euvalennn/beagle/pcb/assets/bfp.png

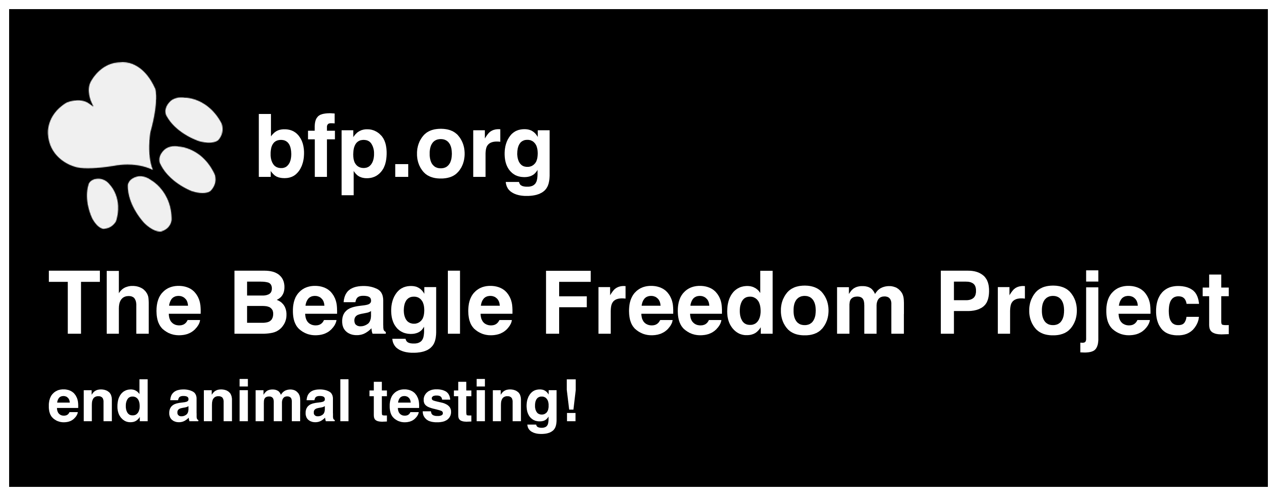
pcb/assets/bfp.png
