euvalennn/beagle/pcb/assets/borders.png

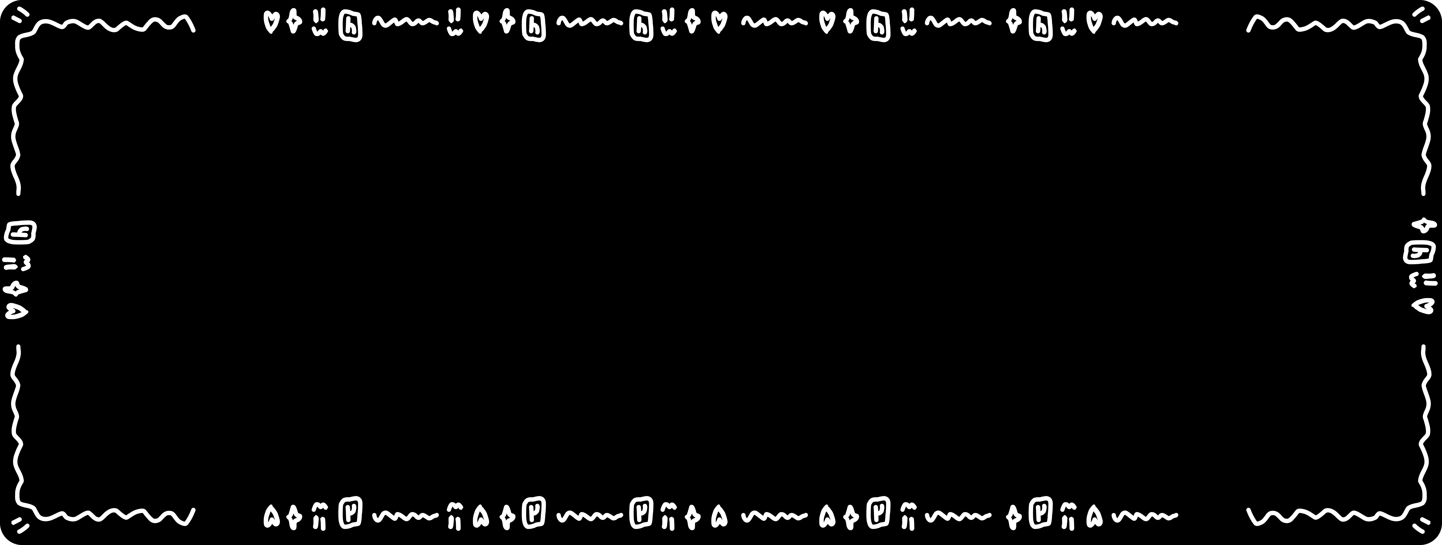
pcb/assets/borders.png
