euvalennn/beagle/pcb/assets/front.png

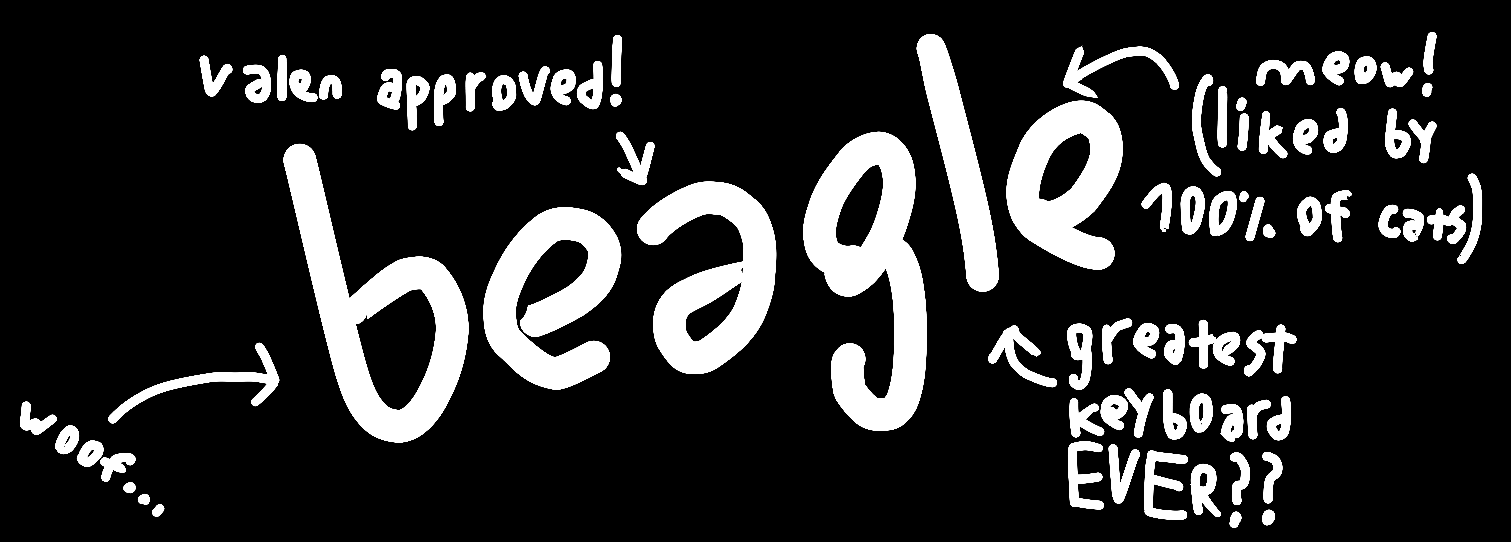
pcb/assets/front.png
