euvalennn/beagle/pcb/assets/stickers.png

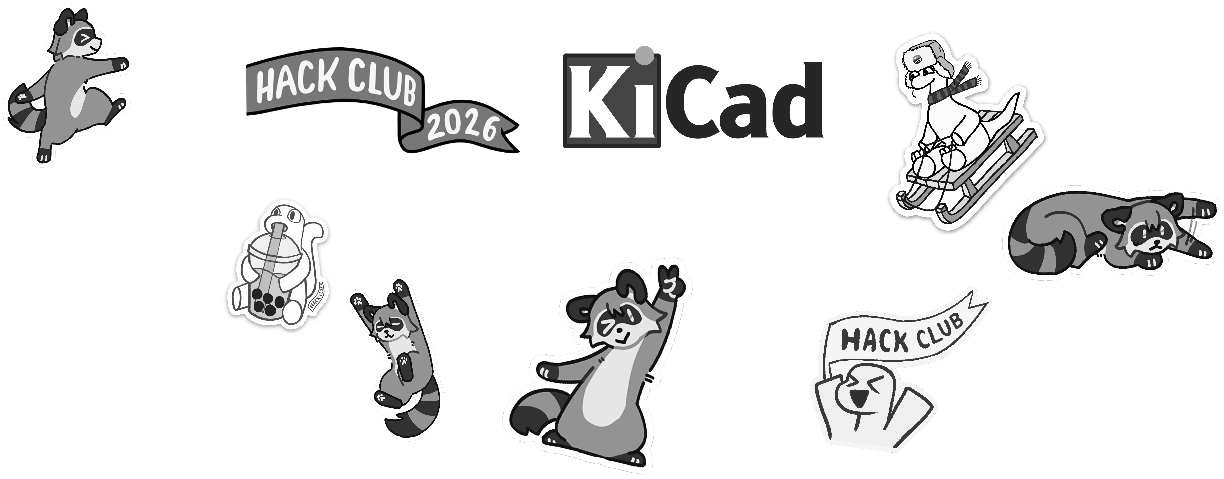
pcb/assets/stickers.png
