euvalennn/beagle/pcb/assets/was here!.png

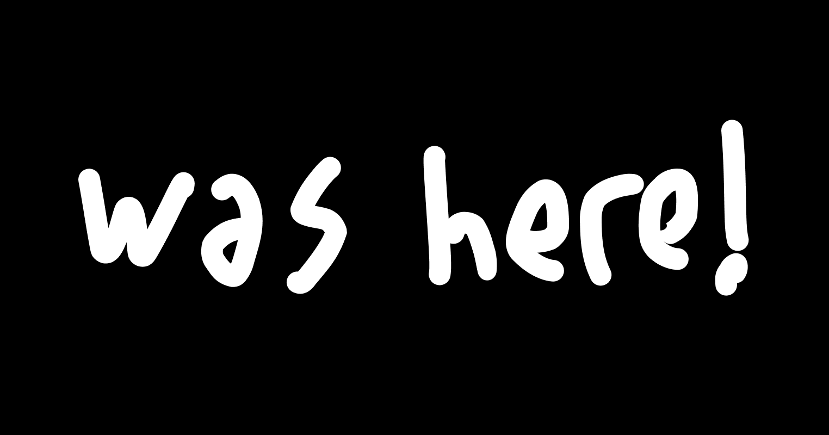
pcb/assets/was here!.png
