euvalennn/beagle/pcb/assets/3dmodels/0.91in OLED Module - Without Glass.stp

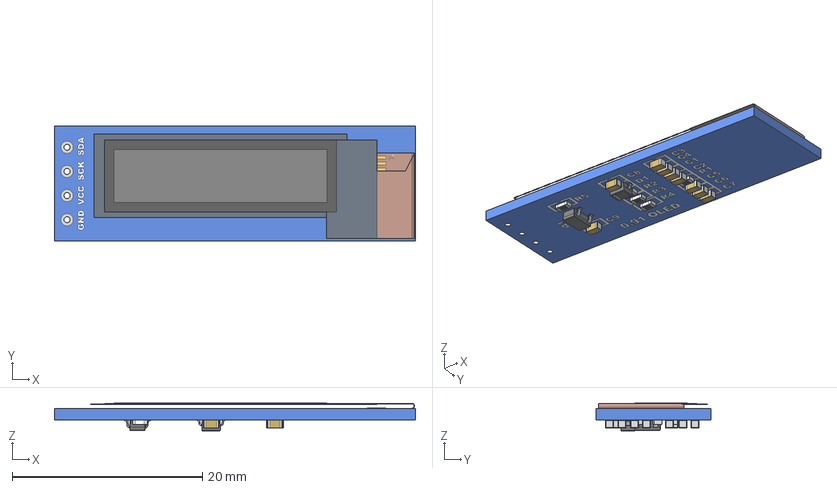
[picture p34: CAD file, 2026-06-26]
pcb/assets/3dmodels/0.91in OLED Module - Without Glass.stp
37.9 x 12.1 x 2.93 mm
0.91in oled Module - Board
0.91in OLED - Folded Flush - Without Glass
0603 Capacitor x 9
0603 Resistor x 5
SOT23-3
Diode (SOD-323)
