euvalennn/beagle/pcb/assets/3dmodels/2-54mm-male-pin-header/Step/100mill Male Pin Header_8P_Bk.STEP

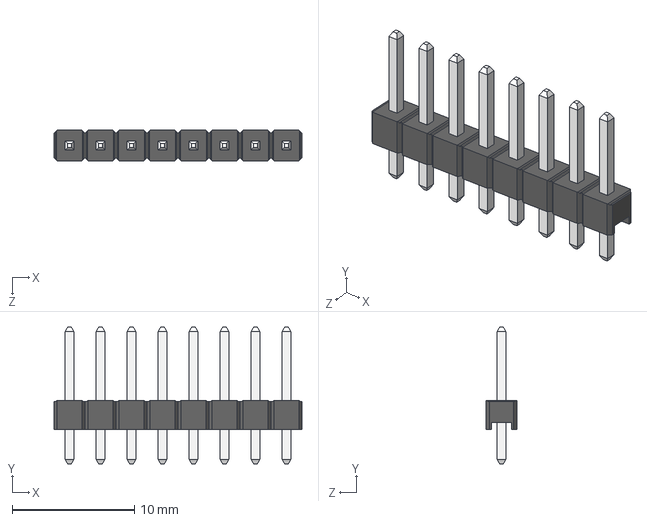
[picture p35: CAD file, 2026-06-26]
pcb/assets/3dmodels/2-54mm-male-pin-header/Step/100mill Male Pin Header_8P_Bk.STEP
20.3 x 11.2 x 2.50 mm
