euvalennn/beagle/pcb/assets/3dmodels/cherry_mx_keycaps/r3/r3_100_bar.STEP

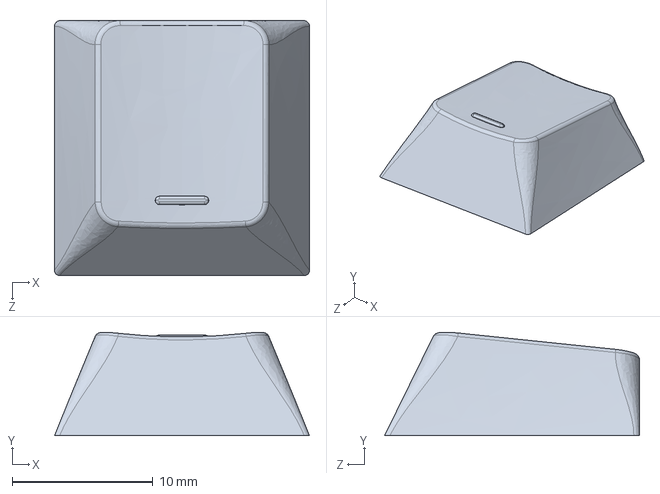
[picture p36: CAD file, 2026-06-26]
pcb/assets/3dmodels/cherry_mx_keycaps/r3/r3_100_bar.STEP
18.1 x 7.34 x 18.1 mm
