euvalennn/beagle/pcb/assets/3dmodels/cherry_mx_keycaps/r4/r3-4_200vert.STEP

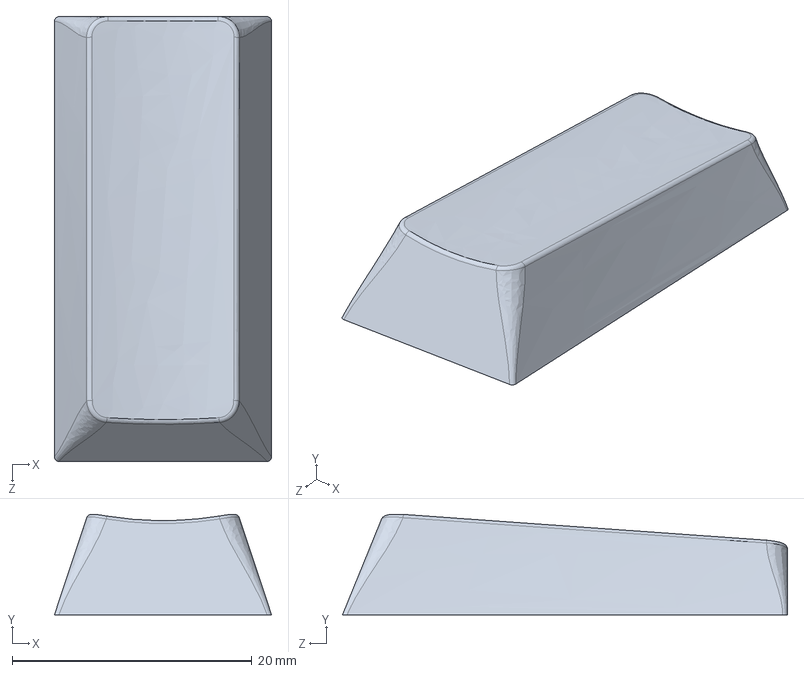
[picture p37: CAD file, 2026-06-26]
pcb/assets/3dmodels/cherry_mx_keycaps/r4/r3-4_200vert.STEP
18.1 x 8.38 x 37.1 mm
