euvalennn/beagle/production/top-case.stl

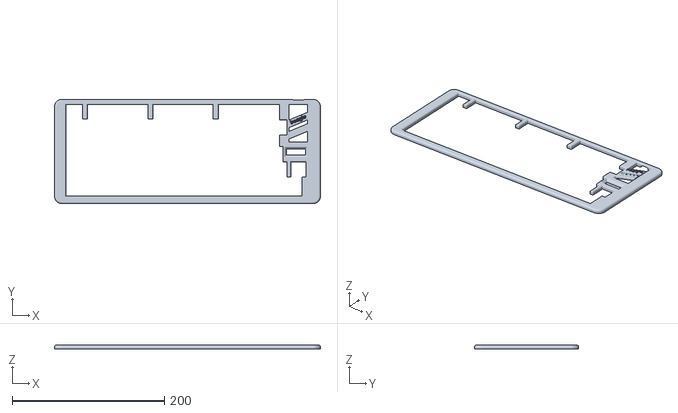
[picture p38: CAD file, 2026-06-26]
production/top-case.stl
349.0 x 137.1 x 5.00
