euvalennn/beagle/pcb/assets/3dmodels/2-54mm-male-pin-header/Step/100mill Male Pin Header_40P_Y.STEP

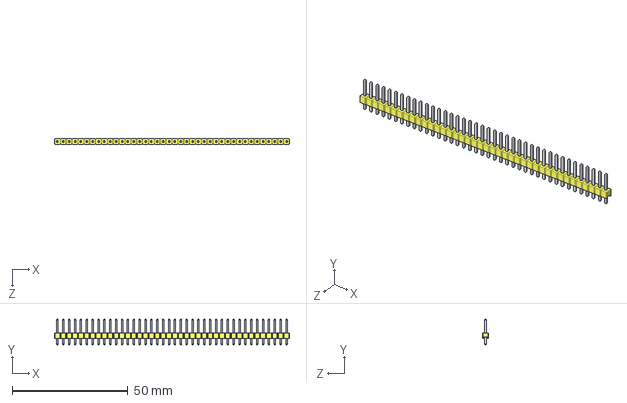
[picture p39: CAD file, 2026-06-26]
pcb/assets/3dmodels/2-54mm-male-pin-header/Step/100mill Male Pin Header_40P_Y.STEP
101.6 x 11.2 x 2.50 mm
