euvalennn/beagle/pcb/assets/3dmodels/cherry_mx_keycaps/r3/r3_200.STEP

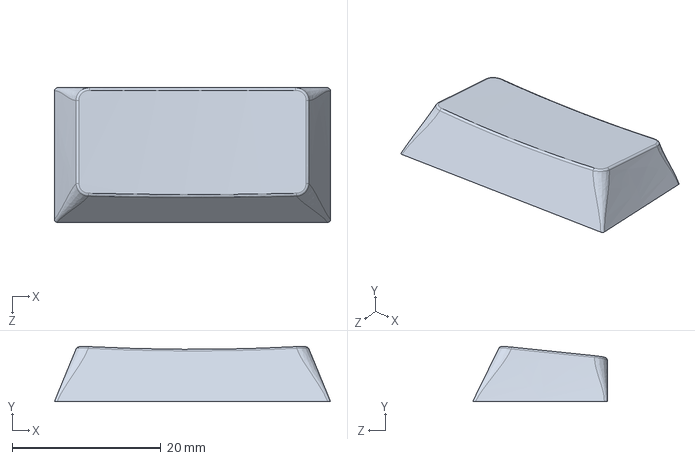
[picture p40: CAD file, 2026-06-26]
pcb/assets/3dmodels/cherry_mx_keycaps/r3/r3_200.STEP
37.1 x 7.40 x 18.1 mm
