euvalennn/beagle/pcb/assets/3dmodels/cherry_mx_keycaps/r4/r4_275C.step

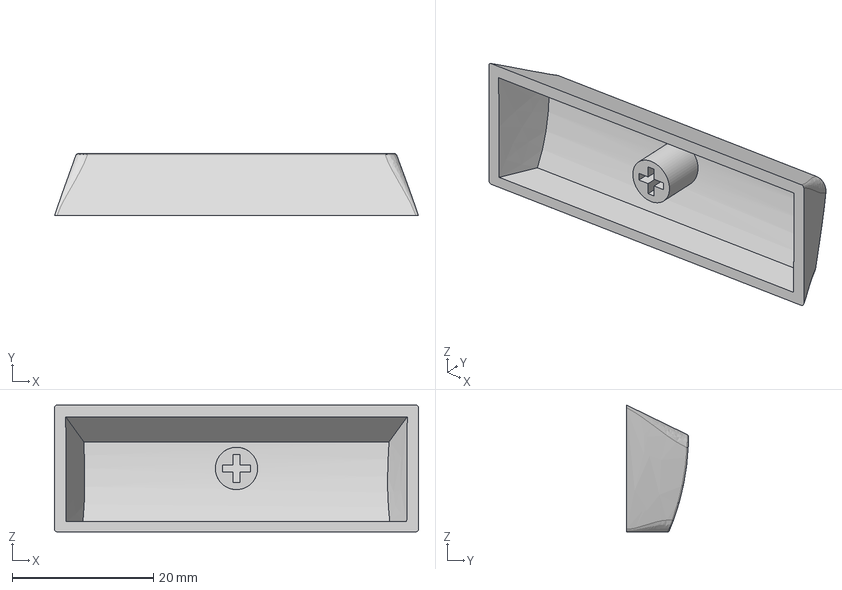
[picture p41: CAD file, 2026-06-26]
pcb/assets/3dmodels/cherry_mx_keycaps/r4/r4_275C.step
51.6 x 8.80 x 18.0 mm
