euvalennn/beagle/pcb/assets/3dmodels/hc-knob.step

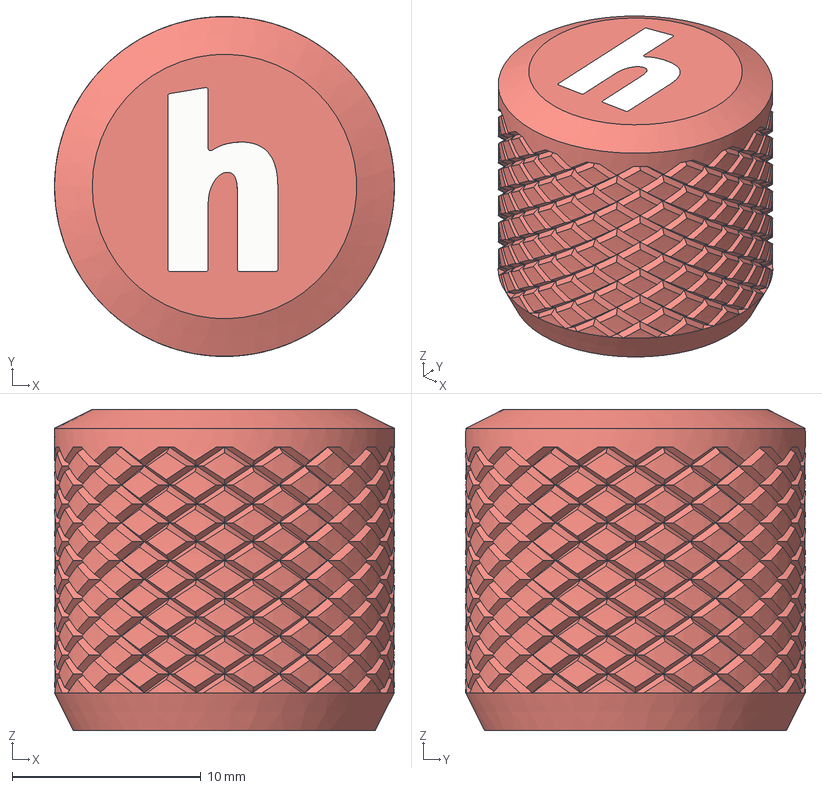
[picture p42: CAD file, 2026-06-26]
pcb/assets/3dmodels/hc-knob.step
18.0 x 18.0 x 17.0 mm
Base
H
