euvalennn/beagle/production/plate.stl

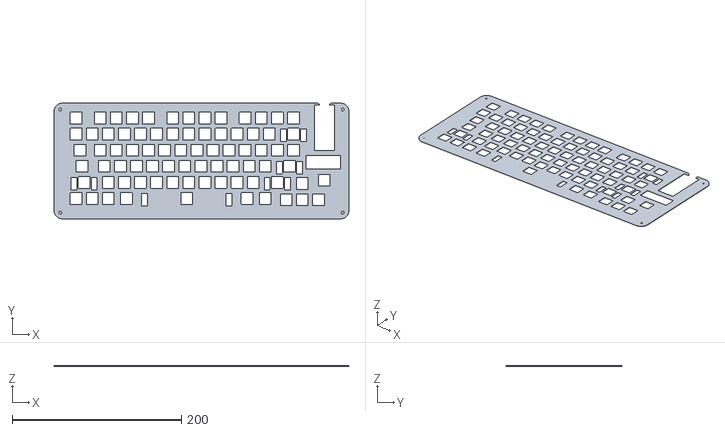
[picture p43: CAD file, 2026-06-26]
production/plate.stl
349.0 x 137.1 x 1.50
