euvalennn/beagle/pcb/assets/3dmodels/2-54mm-male-pin-header/Step/100mill Male Pin Header_4P_R.STEP

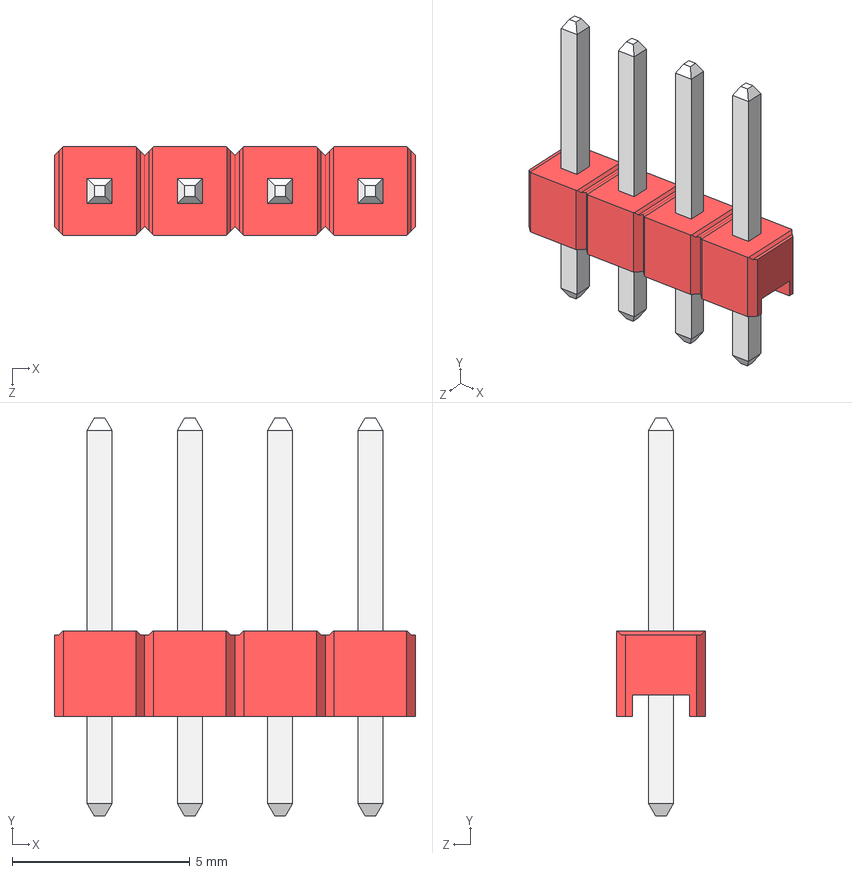
[picture p44: CAD file, 2026-06-26]
pcb/assets/3dmodels/2-54mm-male-pin-header/Step/100mill Male Pin Header_4P_R.STEP
10.2 x 11.2 x 2.50 mm
