euvalennn/beagle/pcb/assets/3dmodels/cherry_mx_keycaps/r4/r4_100.STEP

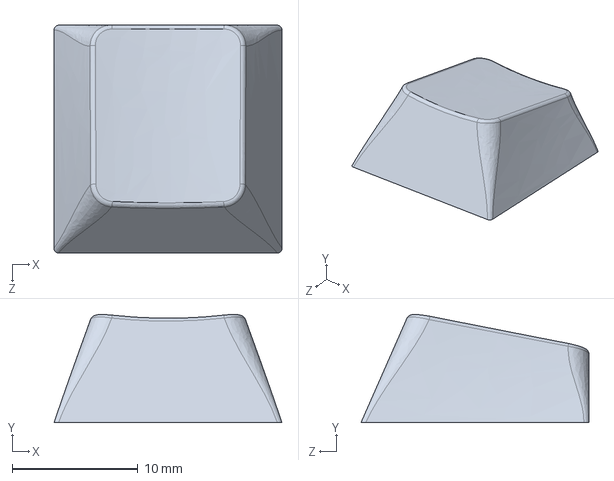
[picture p45: CAD file, 2026-06-26]
pcb/assets/3dmodels/cherry_mx_keycaps/r4/r4_100.STEP
18.1 x 8.58 x 18.1 mm
