euvalennn/beagle/pcb/assets/3dmodels/cherry_mx_keycaps/r3/r3_125.STEP

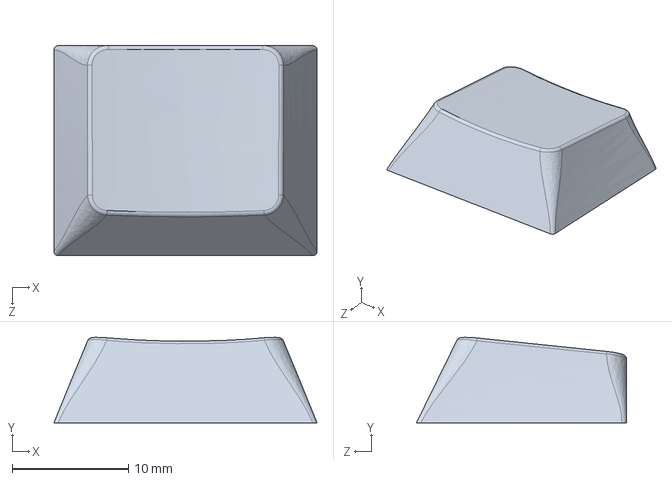
[picture p47: CAD file, 2026-06-26]
pcb/assets/3dmodels/cherry_mx_keycaps/r3/r3_125.STEP
22.7 x 7.36 x 18.1 mm
