euvalennn/beagle/pcb/assets/3dmodels/cherry_mx_keycaps/r4/r4_200C.step

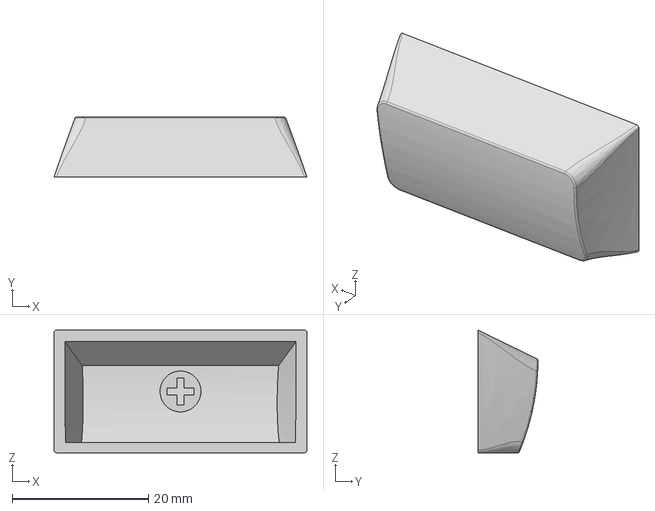
[picture p48: CAD file, 2026-06-26]
pcb/assets/3dmodels/cherry_mx_keycaps/r4/r4_200C.step
37.1 x 8.80 x 18.0 mm
