euvalennn/beagle/pcb/assets/3dmodels/cherry_mx_keycaps/r3/r3_iso.STEP

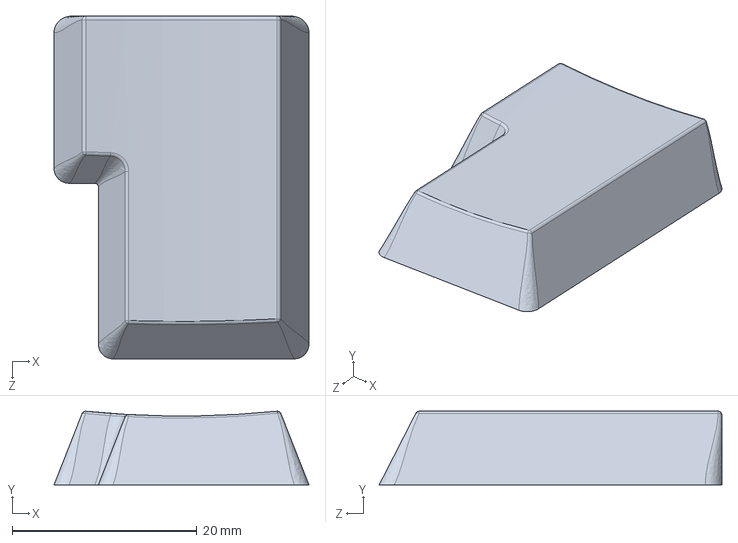
[picture p50: CAD file, 2026-06-26]
pcb/assets/3dmodels/cherry_mx_keycaps/r3/r3_iso.STEP
27.6 x 7.97 x 37.1 mm
