euvalennn/beagle/pcb/assets/3dmodels/cherry_mx_keycaps/r4/r4_100C.step

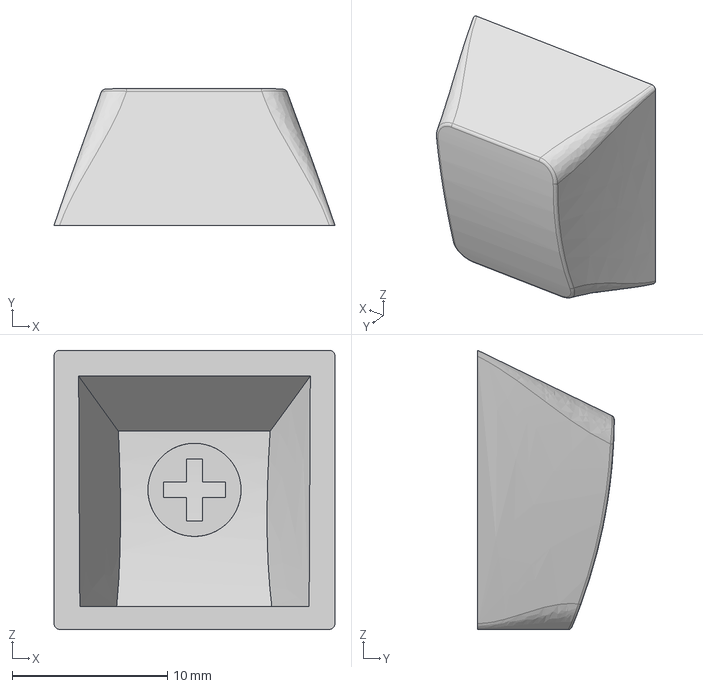
[picture p51: CAD file, 2026-06-26]
pcb/assets/3dmodels/cherry_mx_keycaps/r4/r4_100C.step
18.1 x 8.80 x 18.0 mm
