euvalennn/beagle/pcb/assets/3dmodels/cherry_mx_keycaps/r3/r3_175_stepped.STEP

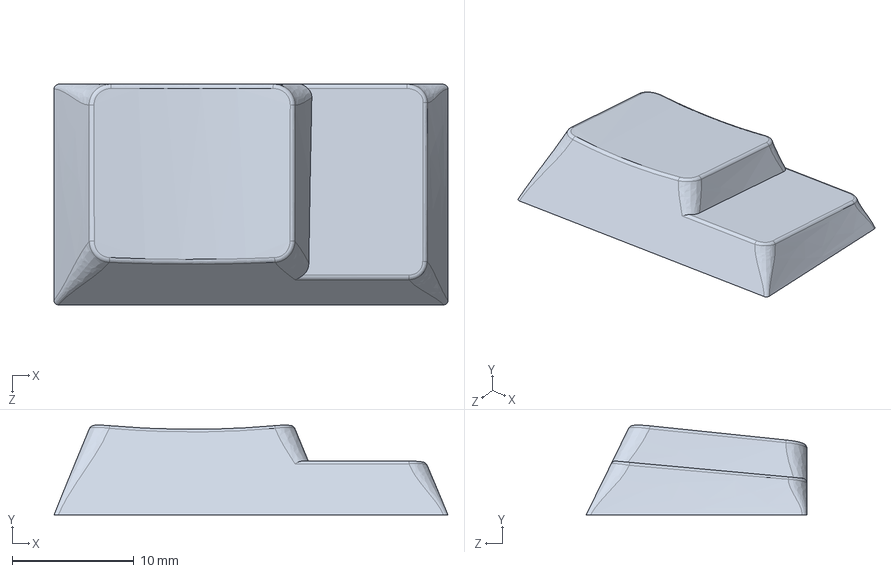
[picture p53: CAD file, 2026-06-26]
pcb/assets/3dmodels/cherry_mx_keycaps/r3/r3_175_stepped.STEP
32.3 x 7.36 x 18.1 mm
