euvalennn/beagle/pcb/assets/3dmodels/cherry_mx_keycaps/r4/r4_175.STEP

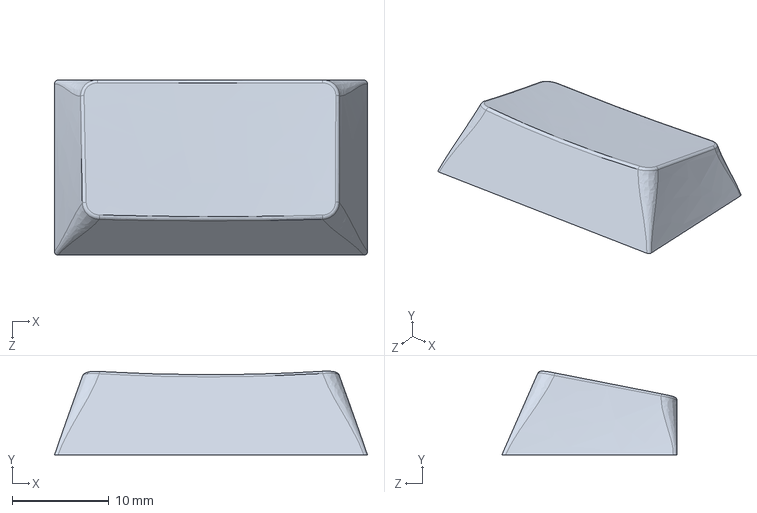
[picture p54: CAD file, 2026-06-26]
pcb/assets/3dmodels/cherry_mx_keycaps/r4/r4_175.STEP
32.3 x 8.65 x 18.1 mm
