euvalennn/beagle/pcb/assets/3dmodels/cherry_mx_keycaps/r3/r2-3_200vert.STEP

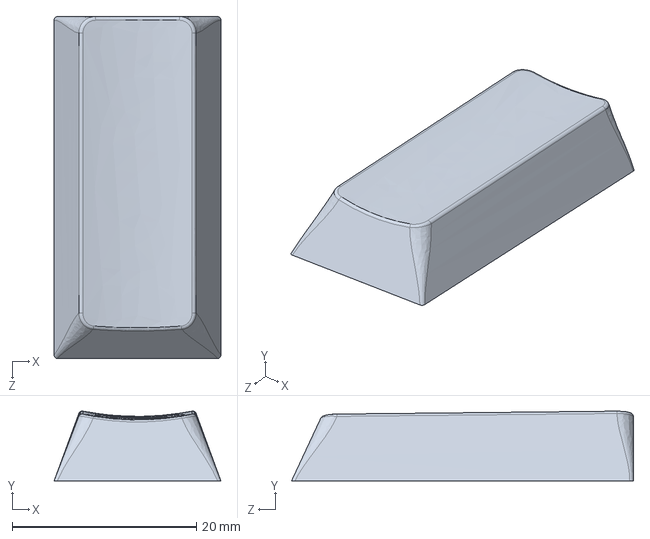
[picture p56: CAD file, 2026-06-26]
pcb/assets/3dmodels/cherry_mx_keycaps/r3/r2-3_200vert.STEP
18.1 x 7.57 x 37.1 mm
