euvalennn/beagle/pcb/assets/3dmodels/cherry_mx_keycaps/r4/r4_275.STEP

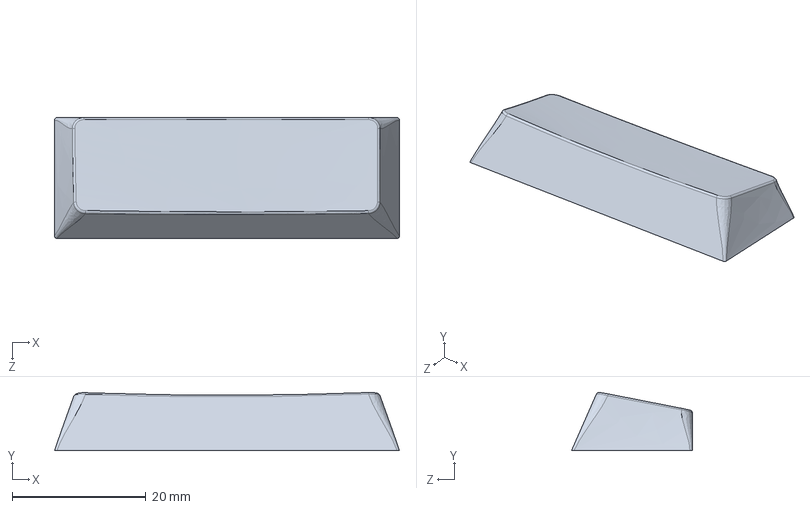
[picture p57: CAD file, 2026-06-26]
pcb/assets/3dmodels/cherry_mx_keycaps/r4/r4_275.STEP
51.6 x 8.69 x 18.1 mm
