euvalennn/beagle/pcb/assets/3dmodels/cherry_mx_keycaps/r3/r3_225.STEP

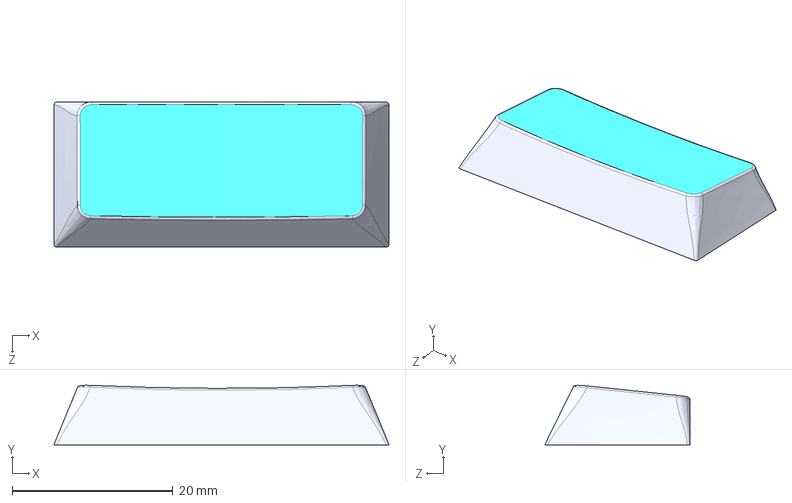
[picture p58: CAD file, 2026-06-26]
pcb/assets/3dmodels/cherry_mx_keycaps/r3/r3_225.STEP
41.7 x 7.41 x 18.1 mm
