euvalennn/beagle/pcb/assets/3dmodels/cherry_mx_keycaps/r4/r4_625.STEP

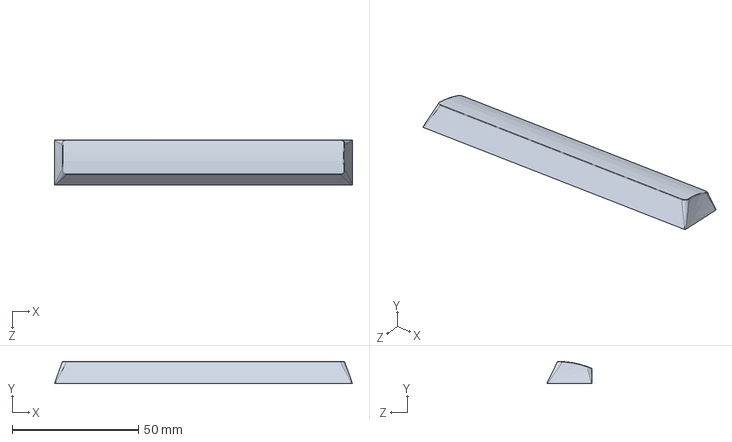
[picture p59: CAD file, 2026-06-26]
pcb/assets/3dmodels/cherry_mx_keycaps/r4/r4_625.STEP
118.1 x 8.80 x 18.0 mm
