euvalennn/beagle/pcb/assets/3dmodels/cherry_mx_keycaps/r3/r3_175.STEP

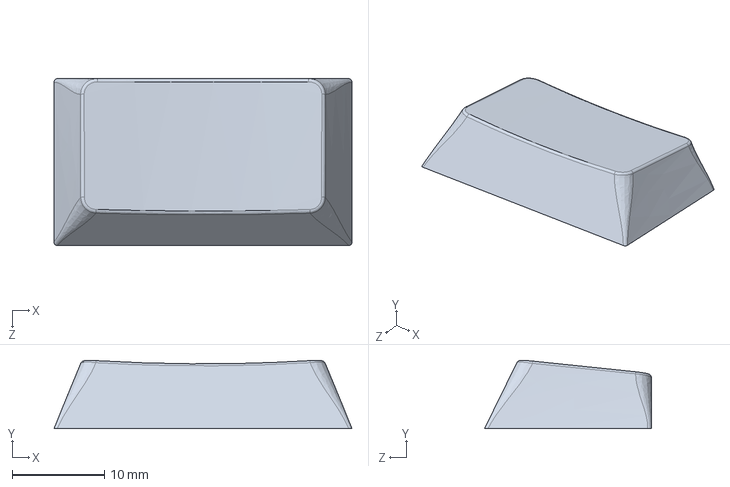
[picture p61: CAD file, 2026-06-26]
pcb/assets/3dmodels/cherry_mx_keycaps/r3/r3_175.STEP
32.3 x 7.39 x 18.1 mm
