euvalennn/beagle/pcb/assets/3dmodels/cherry_mx_keycaps/r4/r4_300C.step

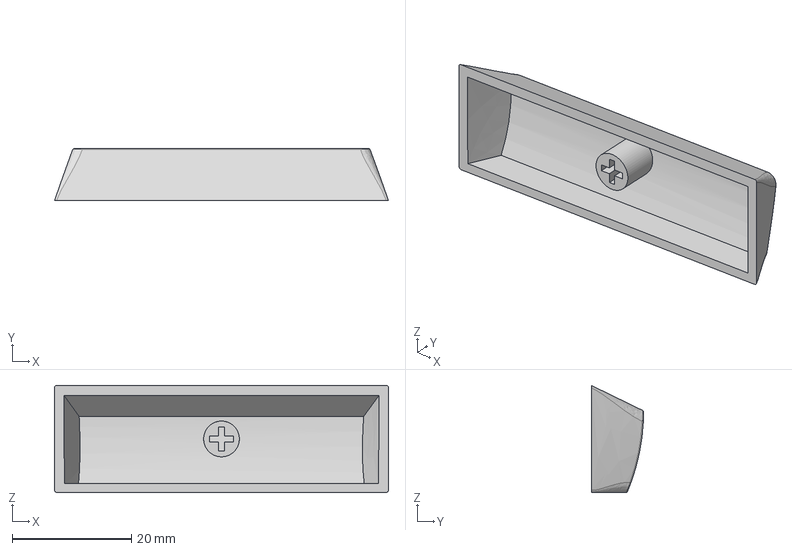
[picture p62: CAD file, 2026-06-26]
pcb/assets/3dmodels/cherry_mx_keycaps/r4/r4_300C.step
56.1 x 8.80 x 18.0 mm
