euvalennn/beagle/pcb/assets/3dmodels/cherry_mx_keycaps/r4/r4_225.STEP

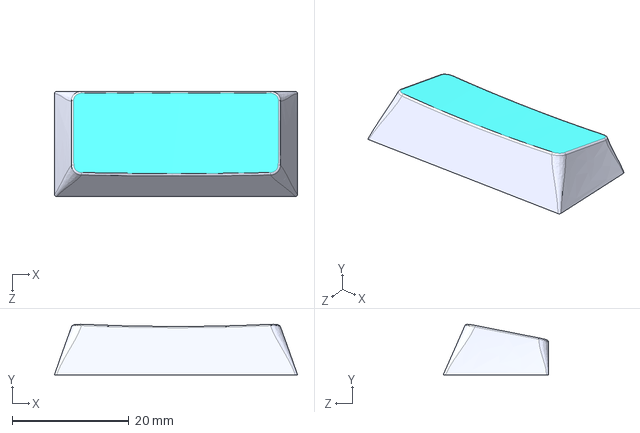
[picture p63: CAD file, 2026-06-26]
pcb/assets/3dmodels/cherry_mx_keycaps/r4/r4_225.STEP
41.7 x 8.67 x 18.1 mm
