euvalennn/beagle/pcb/assets/3dmodels/cherry_mx_keycaps/r4/r4_225C.step

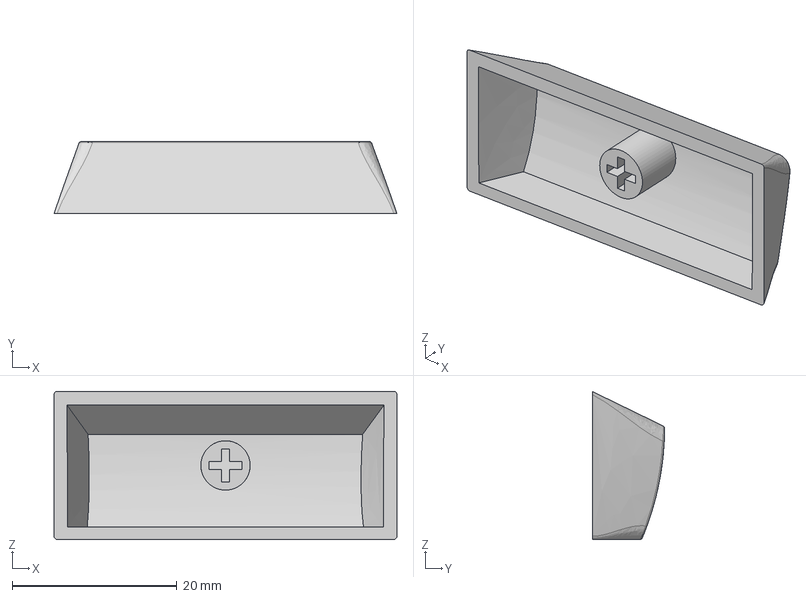
[picture p64: CAD file, 2026-06-26]
pcb/assets/3dmodels/cherry_mx_keycaps/r4/r4_225C.step
41.7 x 8.80 x 18.0 mm
