euvalennn/beagle/pcb/assets/3dmodels/cherry_mx_keycaps/r4/r4_200.STEP

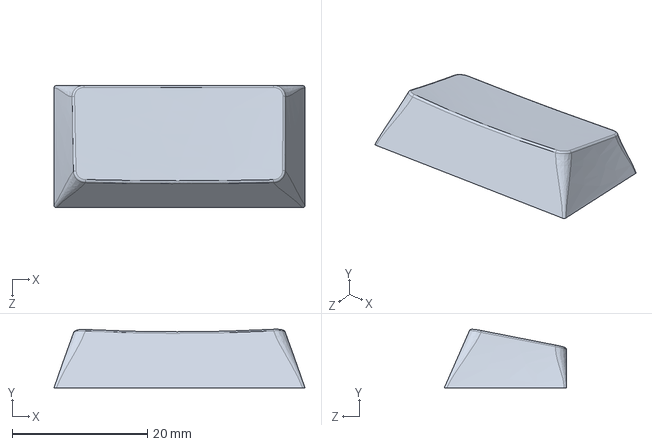
[picture p66: CAD file, 2026-06-26]
pcb/assets/3dmodels/cherry_mx_keycaps/r4/r4_200.STEP
37.1 x 8.66 x 18.1 mm
