euvalennn/beagle/pcb/assets/3dmodels/cherry_mx_keycaps/r4/r4_175C.step

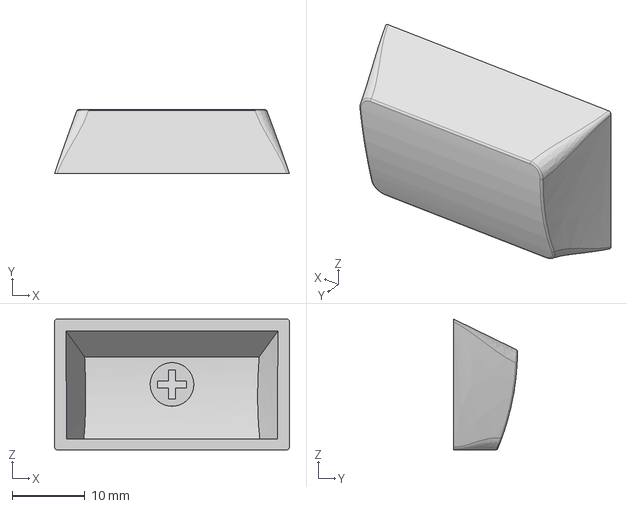
[picture p68: CAD file, 2026-06-26]
pcb/assets/3dmodels/cherry_mx_keycaps/r4/r4_175C.step
32.3 x 8.80 x 18.0 mm
