euvalennn/beagle/pcb/assets/3dmodels/cherry_mx_keycaps/r4/r4_700.STEP

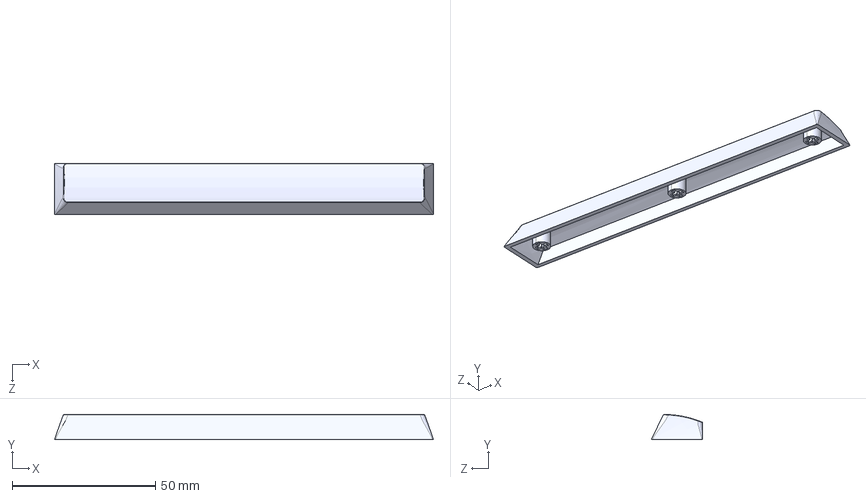
[picture p69: CAD file, 2026-06-26]
pcb/assets/3dmodels/cherry_mx_keycaps/r4/r4_700.STEP
132.5 x 8.80 x 18.0 mm
