euvalennn/beagle/pcb/assets/3dmodels/cherry_mx_keycaps/r4/r4_125.STEP

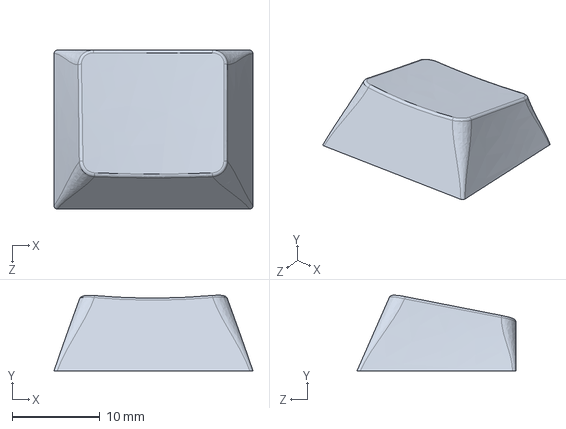
[picture p70: CAD file, 2026-06-26]
pcb/assets/3dmodels/cherry_mx_keycaps/r4/r4_125.STEP
22.7 x 8.61 x 18.1 mm
