euvalennn/beagle/pcb/assets/3dmodels/2-54mm-male-pin-header/Step/100mill Male Pin Header_20P_Bk.STEP

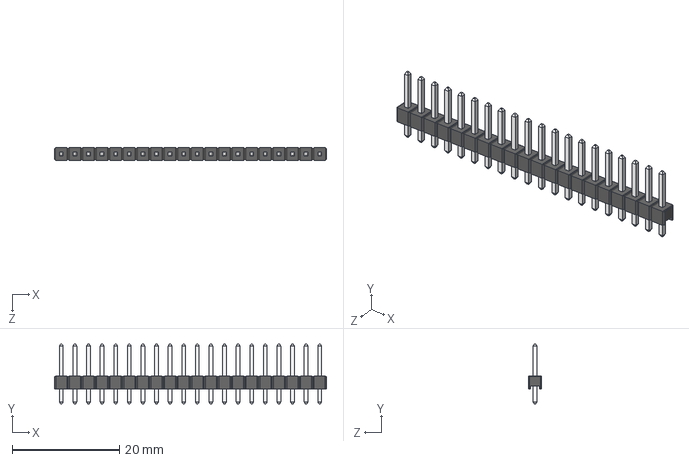
[picture p71: CAD file, 2026-06-26]
pcb/assets/3dmodels/2-54mm-male-pin-header/Step/100mill Male Pin Header_20P_Bk.STEP
50.8 x 11.2 x 2.50 mm
