euvalennn/beagle/pcb/beagle.kicad_sch

## KiCad design pcb/beagle.kicad_sch (2026-06-26)

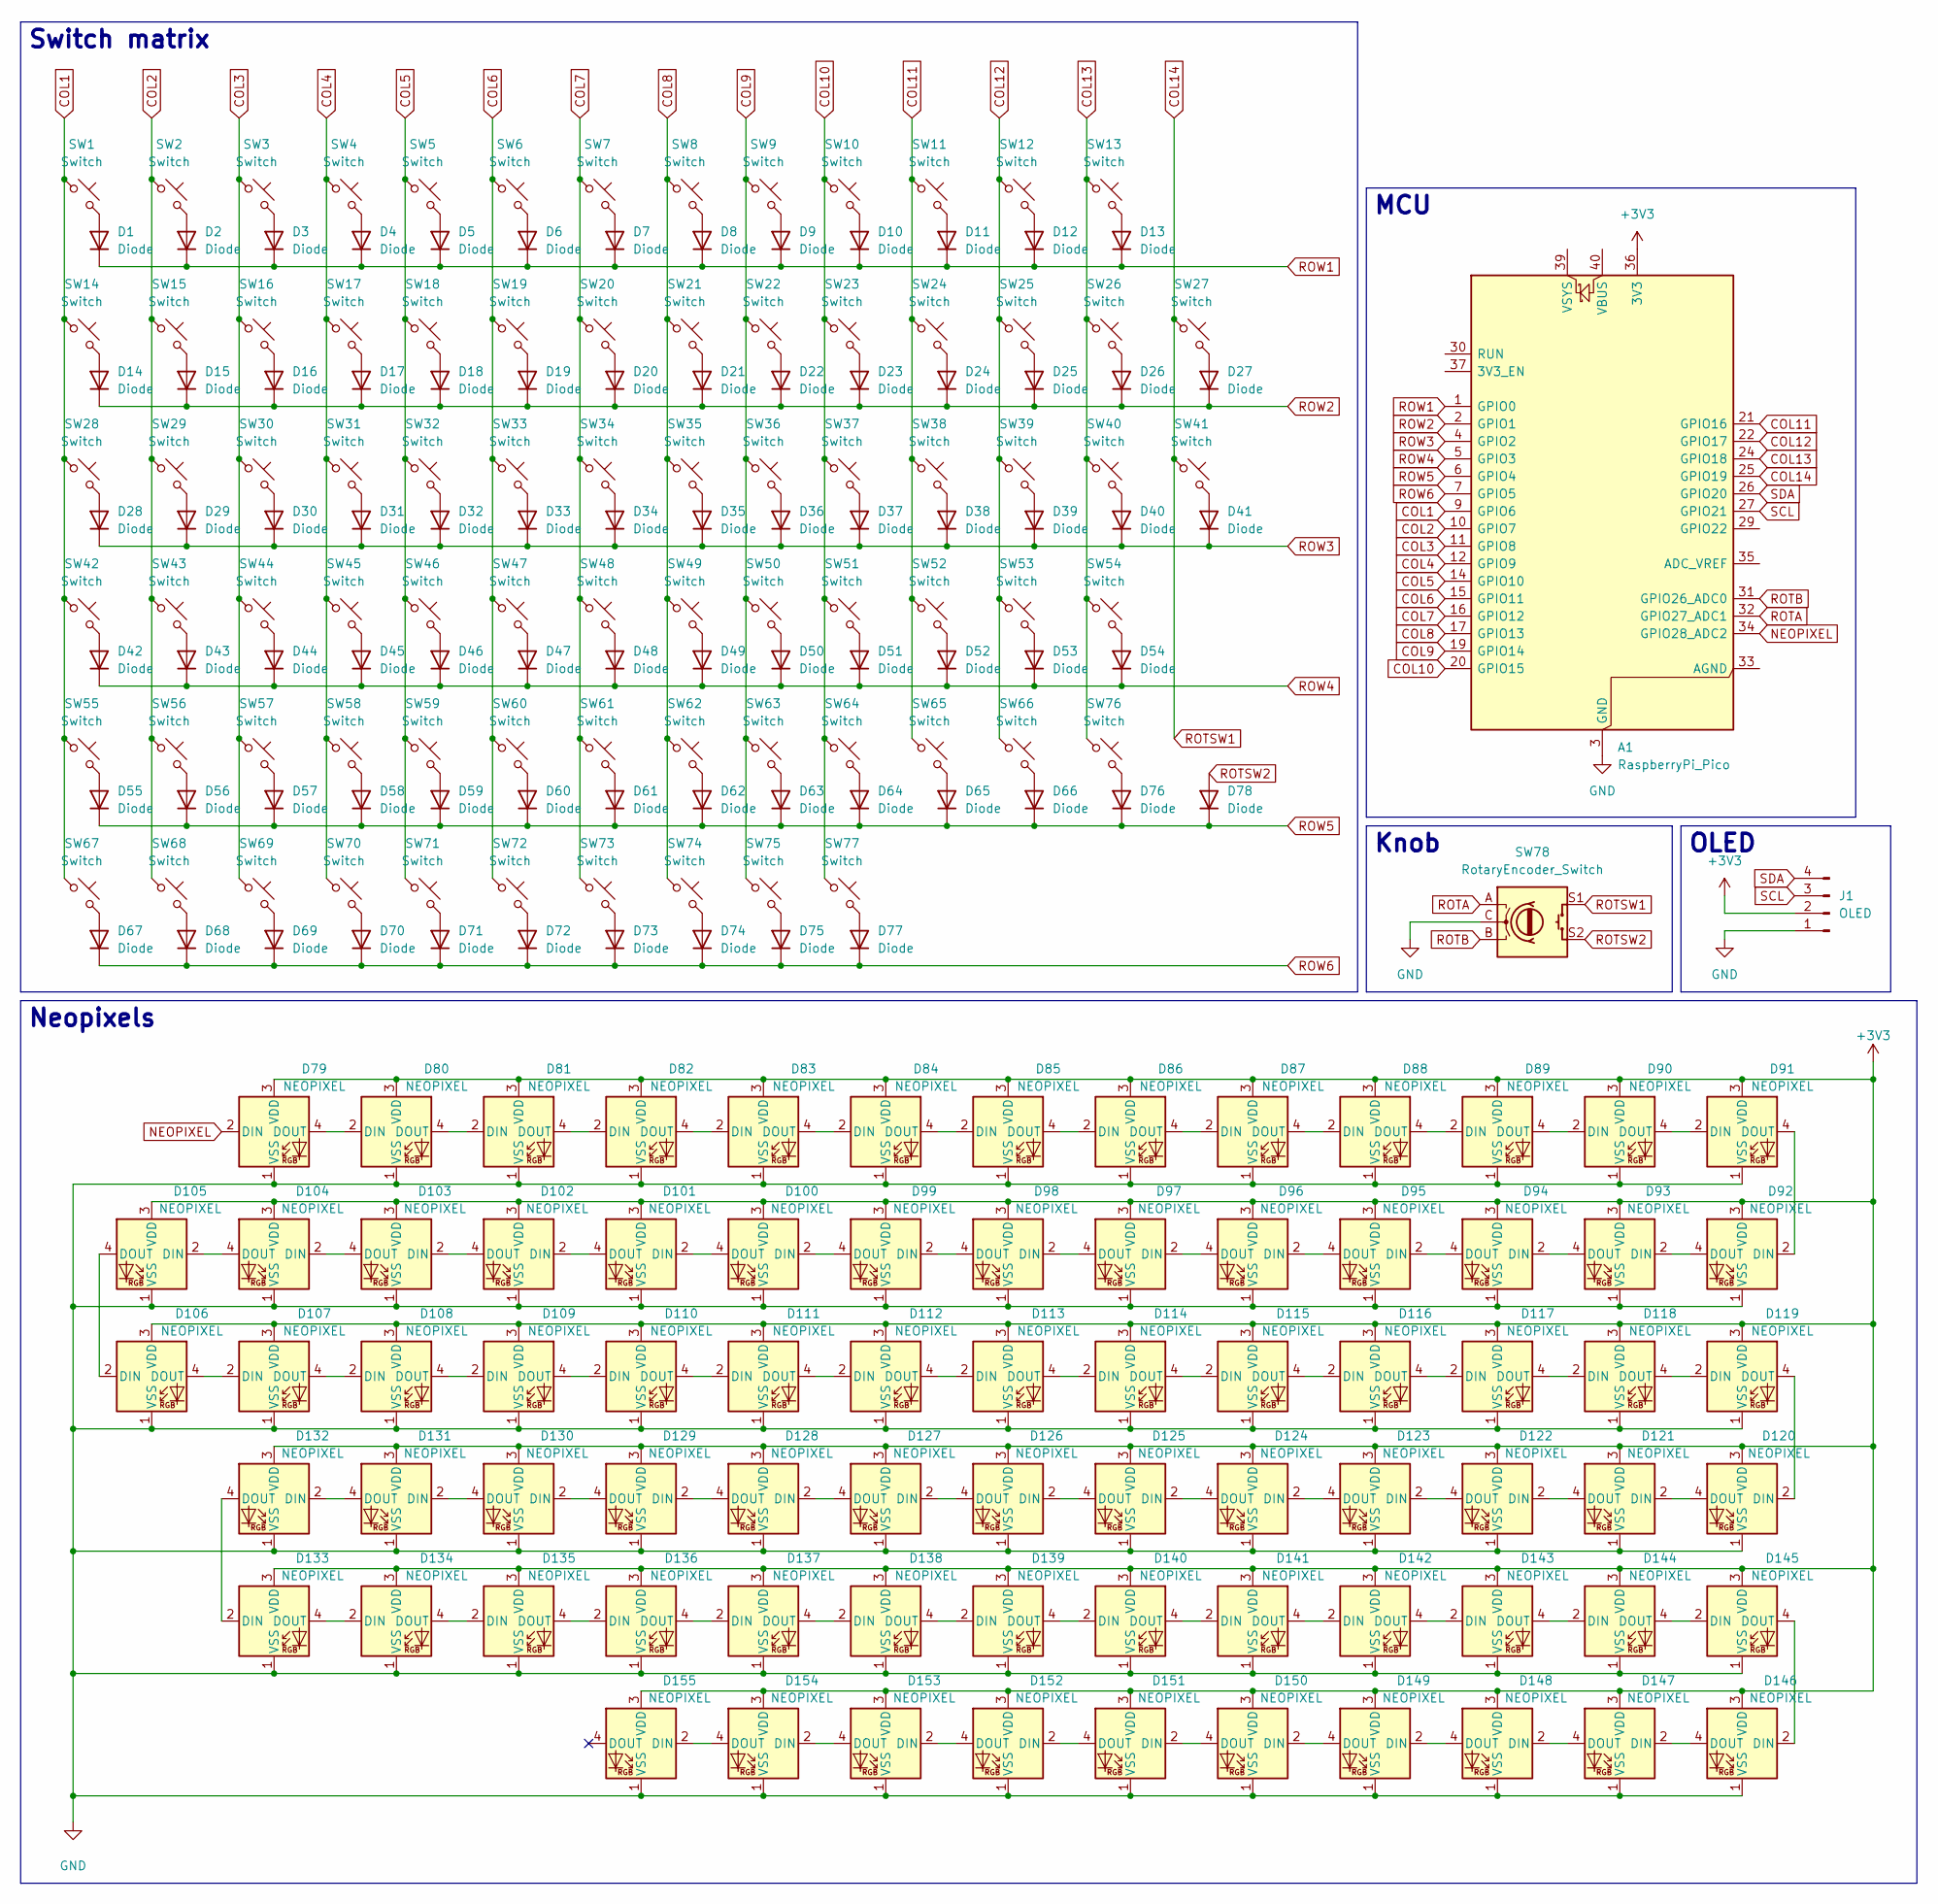
[picture p116: schematic beagle.kicad_sch]

Parts:
A1: RaspberryPi_Pico; RaspberryPi_Pico_Common_Unspecified
D1, D2, D3, D4, D5, D6, D7, D8, D9, D10, D11, D12, D13, D14, D15, D16, D17, D18, D19, D20, D21, D22, D23, D24, D25, D26, D27, D28, D29, D30, D31, D32, D33, D34, D35, D36, D37, D38, D39, D40, D41, D42, D43, D44, D45, D46, D47, D48, D49, D50, D51, D52, D53, D54, D55, D56, D57, D58, D59, D60, D61, D62, D63, D64, D65, D66, D67, D68, D69, D70, D71, D72, D73, D74, D75, D76, D77, D78: Diode; D_DO-35_SOD27_P7.62mm_Horizontal
D79, D80, D81, D82, D83, D84, D85, D86, D87, D88, D89, D90, D91, D92, D93, D94, D95, D96, D97, D98, D99, D100, D101, D102, D103, D104, D105, D106, D107, D108, D109, D110, D111, D112, D113, D114, D115, D116, D117, D118, D119, D120, D121, D122, D123, D124, D125, D126, D127, D128, D129, D130, D131, D132, D133, D134, D135, D136, D137, D138, D139, D140, D141, D142, D143, D144, D145, D146, D147, D148, D149, D150, D151, D152, D153, D154, D155: NEOPIXEL; LED_SK6812MINI-E_3.2x2.8mm_P1.5mm_ReverseMount
J1: OLED; SSD1306-0.91-OLED
SW1, SW2, SW3, SW4, SW5, SW6, SW7, SW8, SW9, SW10, SW11, SW12, SW13, SW14, SW15, SW16, SW17, SW18, SW19, SW20, SW21, SW22, SW23, SW24, SW25, SW26, SW29, SW30, SW31, SW32, SW33, SW34, SW35, SW36, SW37, SW38, SW39, SW40, SW41, SW43, SW44, SW45, SW46, SW47, SW48, SW49, SW50, SW51, SW52, SW53, SW56, SW57, SW58, SW59, SW60, SW61, SW62, SW63, SW64, SW65, SW67, SW68, SW69, SW73, SW74, SW75, SW76, SW77: Switch; SW_Cherry_MX_PCB_1.00u
SW27, SW54, SW55, SW66: Switch; SW_Cherry_MX_PCB_2.00u
SW28: Switch; SW_Cherry_MX_PCB_1.50u
SW42: Switch; SW_Cherry_MX_PCB_1.75u
SW70, SW72: Switch; SW_Cherry_MX_PCB_1.25u
SW71: Switch; SW_Cherry_MX_PCB_6.25u
SW78: RotaryEncoder_Switch; RotaryEncoder_Alps_EC11E-Switch_Vertical_H20mm

Connections:
+3V3: A1.36 (3V3), D79.3 (VDD), D80.3 (VDD), D81.3 (VDD), D82.3 (VDD), D83.3 (VDD), D84.3 (VDD), D85.3 (VDD), D86.3 (VDD), D87.3 (VDD), D88.3 (VDD), D89.3 (VDD), D90.3 (VDD), D91.3 (VDD), D92.3 (VDD), D93.3 (VDD), D94.3 (VDD), D95.3 (VDD), D96.3 (VDD), D97.3 (VDD), D98.3 (VDD), D99.3 (VDD), D100.3 (VDD), D101.3 (VDD), D102.3 (VDD), D103.3 (VDD), D104.3 (VDD), D105.3 (VDD), D106.3 (VDD), D107.3 (VDD), D108.3 (VDD), D109.3 (VDD), D110.3 (VDD), D111.3 (VDD), D112.3 (VDD), D113.3 (VDD), D114.3 (VDD), D115.3 (VDD), D116.3 (VDD), D117.3 (VDD), D118.3 (VDD), D119.3 (VDD), D120.3 (VDD), D121.3 (VDD), D122.3 (VDD), D123.3 (VDD), D124.3 (VDD), D125.3 (VDD), D126.3 (VDD), D127.3 (VDD), D128.3 (VDD), D129.3 (VDD), D130.3 (VDD), D131.3 (VDD), D132.3 (VDD), D133.3 (VDD), D134.3 (VDD), D135.3 (VDD), D136.3 (VDD), D137.3 (VDD), D138.3 (VDD), D139.3 (VDD), D140.3 (VDD), D141.3 (VDD), D142.3 (VDD), D143.3 (VDD), D144.3 (VDD), D145.3 (VDD), D146.3 (VDD), D147.3 (VDD), D148.3 (VDD), D149.3 (VDD), D150.3 (VDD), D151.3 (VDD), D152.3 (VDD), D153.3 (VDD), D154.3 (VDD), D155.3 (VDD), J1.2
COL1: A1.9 (GPIO6), SW1.1, SW14.1, SW28.1, SW42.1, SW55.1, SW67.1
COL2: A1.10 (GPIO7), SW2.1, SW15.1, SW29.1, SW43.1, SW56.1, SW68.1
COL3: A1.11 (GPIO8), SW3.1, SW16.1, SW30.1, SW44.1, SW57.1, SW69.1
COL4: A1.12 (GPIO9), SW4.1, SW17.1, SW31.1, SW45.1, SW58.1, SW70.1
COL5: A1.14 (GPIO10), SW5.1, SW18.1, SW32.1, SW46.1, SW59.1, SW71.1
COL6: A1.15 (GPIO11), SW6.1, SW19.1, SW33.1, SW47.1, SW60.1, SW72.1
COL7: A1.16 (GPIO12), SW7.1, SW20.1, SW34.1, SW48.1, SW61.1, SW73.1
COL8: A1.17 (GPIO13), SW8.1, SW21.1, SW35.1, SW49.1, SW62.1, SW74.1
COL9: A1.19 (GPIO14), SW9.1, SW22.1, SW36.1, SW50.1, SW63.1, SW75.1
COL10: A1.20 (GPIO15), SW10.1, SW23.1, SW37.1, SW51.1, SW64.1, SW77.1
COL11: A1.21 (GPIO16), SW11.1, SW24.1, SW38.1, SW52.1, SW65.1
COL12: A1.22 (GPIO17), SW12.1, SW25.1, SW39.1, SW53.1, SW66.1
COL13: A1.24 (GPIO18), SW13.1, SW26.1, SW40.1, SW54.1, SW76.1
COL14: A1.25 (GPIO19), SW27.1, SW41.1, SW78.S1
GND: A1.3 (GND), A1.8 (GND), A1.13 (GND), A1.18 (GND), A1.23 (GND), A1.28 (GND), A1.38 (GND), D79.1 (VSS), D80.1 (VSS), D81.1 (VSS), D82.1 (VSS), D83.1 (VSS), D84.1 (VSS), D85.1 (VSS), D86.1 (VSS), D87.1 (VSS), D88.1 (VSS), D89.1 (VSS), D90.1 (VSS), D91.1 (VSS), D92.1 (VSS), D93.1 (VSS), D94.1 (VSS), D95.1 (VSS), D96.1 (VSS), D97.1 (VSS), D98.1 (VSS), D99.1 (VSS), D100.1 (VSS), D101.1 (VSS), D102.1 (VSS), D103.1 (VSS), D104.1 (VSS), D105.1 (VSS), D106.1 (VSS), D107.1 (VSS), D108.1 (VSS), D109.1 (VSS), D110.1 (VSS), D111.1 (VSS), D112.1 (VSS), D113.1 (VSS), D114.1 (VSS), D115.1 (VSS), D116.1 (VSS), D117.1 (VSS), D118.1 (VSS), D119.1 (VSS), D120.1 (VSS), D121.1 (VSS), D122.1 (VSS), D123.1 (VSS), D124.1 (VSS), D125.1 (VSS), D126.1 (VSS), D127.1 (VSS), D128.1 (VSS), D129.1 (VSS), D130.1 (VSS), D131.1 (VSS), D132.1 (VSS), D133.1 (VSS), D134.1 (VSS), D135.1 (VSS), D136.1 (VSS), D137.1 (VSS), D138.1 (VSS), D139.1 (VSS), D140.1 (VSS), D141.1 (VSS), D142.1 (VSS), D143.1 (VSS), D144.1 (VSS), D145.1 (VSS), D146.1 (VSS), D147.1 (VSS), D148.1 (VSS), D149.1 (VSS), D150.1 (VSS), D151.1 (VSS), D152.1 (VSS), D153.1 (VSS), D154.1 (VSS), D155.1 (VSS), J1.1, SW78.C
NEOPIXEL: A1.34 (GPIO28_ADC2), D79.2 (DIN)
unnamed: D1.2 (A), SW1.2
unnamed: D2.2 (A), SW2.2
unnamed: D3.2 (A), SW3.2
unnamed: D4.2 (A), SW4.2
unnamed: D5.2 (A), SW5.2
unnamed: D6.2 (A), SW6.2
unnamed: D7.2 (A), SW7.2
unnamed: D8.2 (A), SW8.2
unnamed: D9.2 (A), SW9.2
unnamed: D10.2 (A), SW10.2
unnamed: D11.2 (A), SW11.2
unnamed: D12.2 (A), SW12.2
unnamed: D13.2 (A), SW13.2
unnamed: D14.2 (A), SW14.2
unnamed: D15.2 (A), SW15.2
unnamed: D16.2 (A), SW16.2
unnamed: D17.2 (A), SW17.2
unnamed: D18.2 (A), SW18.2
unnamed: D19.2 (A), SW19.2
unnamed: D20.2 (A), SW20.2
unnamed: D21.2 (A), SW21.2
unnamed: D22.2 (A), SW22.2
unnamed: D23.2 (A), SW23.2
unnamed: D24.2 (A), SW24.2
unnamed: D25.2 (A), SW25.2
unnamed: D26.2 (A), SW26.2
unnamed: D27.2 (A), SW27.2
unnamed: D28.2 (A), SW28.2
unnamed: D29.2 (A), SW29.2
unnamed: D30.2 (A), SW30.2
unnamed: D31.2 (A), SW31.2
unnamed: D32.2 (A), SW32.2
unnamed: D33.2 (A), SW33.2
unnamed: D34.2 (A), SW34.2
unnamed: D35.2 (A), SW35.2
unnamed: D36.2 (A), SW36.2
unnamed: D37.2 (A), SW37.2
unnamed: D38.2 (A), SW38.2
unnamed: D39.2 (A), SW39.2
unnamed: D40.2 (A), SW40.2
unnamed: D41.2 (A), SW41.2
unnamed: D42.2 (A), SW42.2
unnamed: D43.2 (A), SW43.2
unnamed: D44.2 (A), SW44.2
unnamed: D45.2 (A), SW45.2
unnamed: D46.2 (A), SW46.2
unnamed: D47.2 (A), SW47.2
unnamed: D48.2 (A), SW48.2
unnamed: D49.2 (A), SW49.2
unnamed: D50.2 (A), SW50.2
unnamed: D51.2 (A), SW51.2
unnamed: D52.2 (A), SW52.2
unnamed: D53.2 (A), SW53.2
unnamed: D54.2 (A), SW54.2
unnamed: D55.2 (A), SW55.2
unnamed: D56.2 (A), SW56.2
unnamed: D57.2 (A), SW57.2
unnamed: D58.2 (A), SW58.2
unnamed: D59.2 (A), SW59.2
unnamed: D60.2 (A), SW60.2
unnamed: D61.2 (A), SW61.2
unnamed: D62.2 (A), SW62.2
unnamed: D63.2 (A), SW63.2
unnamed: D64.2 (A), SW64.2
unnamed: D65.2 (A), SW65.2
unnamed: D66.2 (A), SW66.2
unnamed: D67.2 (A), SW67.2
unnamed: D68.2 (A), SW68.2
unnamed: D69.2 (A), SW69.2
unnamed: D70.2 (A), SW70.2
unnamed: D71.2 (A), SW71.2
unnamed: D72.2 (A), SW72.2
unnamed: D73.2 (A), SW73.2
unnamed: D74.2 (A), SW74.2
unnamed: D75.2 (A), SW75.2
unnamed: D76.2 (A), SW76.2
unnamed: D77.2 (A), SW77.2
unnamed: D79.4 (DOUT), D80.2 (DIN)
unnamed: D80.4 (DOUT), D81.2 (DIN)
unnamed: D81.4 (DOUT), D82.2 (DIN)
unnamed: D82.4 (DOUT), D83.2 (DIN)
unnamed: D83.4 (DOUT), D84.2 (DIN)
unnamed: D84.4 (DOUT), D85.2 (DIN)
unnamed: D85.4 (DOUT), D86.2 (DIN)
unnamed: D86.4 (DOUT), D87.2 (DIN)
unnamed: D87.4 (DOUT), D88.2 (DIN)
unnamed: D88.4 (DOUT), D89.2 (DIN)
unnamed: D89.4 (DOUT), D90.2 (DIN)
unnamed: D90.4 (DOUT), D91.2 (DIN)
unnamed: D91.4 (DOUT), D92.2 (DIN)
unnamed: D92.4 (DOUT), D93.2 (DIN)
unnamed: D93.4 (DOUT), D94.2 (DIN)
unnamed: D94.4 (DOUT), D95.2 (DIN)
unnamed: D95.4 (DOUT), D96.2 (DIN)
unnamed: D96.4 (DOUT), D97.2 (DIN)
unnamed: D97.4 (DOUT), D98.2 (DIN)
unnamed: D98.4 (DOUT), D99.2 (DIN)
unnamed: D99.4 (DOUT), D100.2 (DIN)
unnamed: D100.4 (DOUT), D101.2 (DIN)
unnamed: D101.4 (DOUT), D102.2 (DIN)
unnamed: D102.4 (DOUT), D103.2 (DIN)
unnamed: D103.4 (DOUT), D104.2 (DIN)
unnamed: D104.4 (DOUT), D105.2 (DIN)
unnamed: D105.4 (DOUT), D106.2 (DIN)
unnamed: D106.4 (DOUT), D107.2 (DIN)
unnamed: D107.4 (DOUT), D108.2 (DIN)
unnamed: D108.4 (DOUT), D109.2 (DIN)
unnamed: D109.4 (DOUT), D110.2 (DIN)
unnamed: D110.4 (DOUT), D111.2 (DIN)
unnamed: D111.4 (DOUT), D112.2 (DIN)
unnamed: D112.4 (DOUT), D113.2 (DIN)
unnamed: D113.4 (DOUT), D114.2 (DIN)
unnamed: D114.4 (DOUT), D115.2 (DIN)
unnamed: D115.4 (DOUT), D116.2 (DIN)
unnamed: D116.4 (DOUT), D117.2 (DIN)
unnamed: D117.4 (DOUT), D118.2 (DIN)
unnamed: D118.4 (DOUT), D119.2 (DIN)
unnamed: D119.4 (DOUT), D120.2 (DIN)
unnamed: D120.4 (DOUT), D121.2 (DIN)
unnamed: D121.4 (DOUT), D122.2 (DIN)
unnamed: D122.4 (DOUT), D123.2 (DIN)
unnamed: D123.4 (DOUT), D124.2 (DIN)
unnamed: D124.4 (DOUT), D125.2 (DIN)
unnamed: D125.4 (DOUT), D126.2 (DIN)
unnamed: D126.4 (DOUT), D127.2 (DIN)
unnamed: D127.4 (DOUT), D128.2 (DIN)
unnamed: D128.4 (DOUT), D129.2 (DIN)
unnamed: D129.4 (DOUT), D130.2 (DIN)
unnamed: D130.4 (DOUT), D131.2 (DIN)
unnamed: D131.4 (DOUT), D132.2 (DIN)
unnamed: D132.4 (DOUT), D133.2 (DIN)
unnamed: D133.4 (DOUT), D134.2 (DIN)
unnamed: D134.4 (DOUT), D135.2 (DIN)
unnamed: D135.4 (DOUT), D136.2 (DIN)
unnamed: D136.4 (DOUT), D137.2 (DIN)
unnamed: D137.4 (DOUT), D138.2 (DIN)
unnamed: D138.4 (DOUT), D139.2 (DIN)
unnamed: D139.4 (DOUT), D140.2 (DIN)
unnamed: D140.4 (DOUT), D141.2 (DIN)
unnamed: D141.4 (DOUT), D142.2 (DIN)
unnamed: D142.4 (DOUT), D143.2 (DIN)
unnamed: D143.4 (DOUT), D144.2 (DIN)
unnamed: D144.4 (DOUT), D145.2 (DIN)
unnamed: D145.4 (DOUT), D146.2 (DIN)
unnamed: D146.4 (DOUT), D147.2 (DIN)
unnamed: D147.4 (DOUT), D148.2 (DIN)
unnamed: D148.4 (DOUT), D149.2 (DIN)
unnamed: D149.4 (DOUT), D150.2 (DIN)
unnamed: D150.4 (DOUT), D151.2 (DIN)
unnamed: D151.4 (DOUT), D152.2 (DIN)
unnamed: D152.4 (DOUT), D153.2 (DIN)
unnamed: D153.4 (DOUT), D154.2 (DIN)
unnamed: D154.4 (DOUT), D155.2 (DIN)
ROTA: A1.32 (GPIO27_ADC1), SW78.A
ROTB: A1.31 (GPIO26_ADC0), SW78.B
ROTSW2: D78.2 (A), SW78.S2
ROW1: A1.1 (GPIO0), D1.1 (K), D2.1 (K), D3.1 (K), D4.1 (K), D5.1 (K), D6.1 (K), D7.1 (K), D8.1 (K), D9.1 (K), D10.1 (K), D11.1 (K), D12.1 (K), D13.1 (K)
ROW2: A1.2 (GPIO1), D14.1 (K), D15.1 (K), D16.1 (K), D17.1 (K), D18.1 (K), D19.1 (K), D20.1 (K), D21.1 (K), D22.1 (K), D23.1 (K), D24.1 (K), D25.1 (K), D26.1 (K), D27.1 (K)
ROW3: A1.4 (GPIO2), D28.1 (K), D29.1 (K), D30.1 (K), D31.1 (K), D32.1 (K), D33.1 (K), D34.1 (K), D35.1 (K), D36.1 (K), D37.1 (K), D38.1 (K), D39.1 (K), D40.1 (K), D41.1 (K)
ROW4: A1.5 (GPIO3), D42.1 (K), D43.1 (K), D44.1 (K), D45.1 (K), D46.1 (K), D47.1 (K), D48.1 (K), D49.1 (K), D50.1 (K), D51.1 (K), D52.1 (K), D53.1 (K), D54.1 (K)
ROW5: A1.6 (GPIO4), D55.1 (K), D56.1 (K), D57.1 (K), D58.1 (K), D59.1 (K), D60.1 (K), D61.1 (K), D62.1 (K), D63.1 (K), D64.1 (K), D65.1 (K), D66.1 (K), D76.1 (K), D78.1 (K)
ROW6: A1.7 (GPIO5), D67.1 (K), D68.1 (K), D69.1 (K), D70.1 (K), D71.1 (K), D72.1 (K), D73.1 (K), D74.1 (K), D75.1 (K), D77.1 (K)
SCL: A1.27 (GPIO21), J1.3
SDA: A1.26 (GPIO20), J1.4

Notes on the sheet:
Neopixels
Knob
Switch matrix
OLED
MCU
